jescarri/lora-sensor/src/lorawan_settings.hpp

#ifndef LORAWAN_SETTINGS_HPP_
#define LORAWAN_SETTINGS_HPP_
#include <FastLED.h>
#include <Preferences.h>
#include <lmic.h>

#include <hal/hal.h>

#define LMIC_PREF_NS_NAME "lmic"
#define LMIC_INIT_NEEDED_KEY_NAME "init"
#define LMIC_BYTES_KEY_NAME "lmic_struct"
#define LORAWAN_CONFIG_PRESENT_KEY "lorawan_config"
#define APP_EUID_KEY "euid"
#define MAX_LORAWAN_CONF_CHAR_LEN 100

#define RW_MODE false
#define RO_MODE true

extern lmic_t SETTINGS_LMIC;
extern Preferences lorawan_preferences;
extern lmic_t LMIC;
extern CRGB leds[1];

void lorawan_preferences_init();
void lmic_save();
bool lmic_init_needed();
void load_lmic();
void resetLmic();
bool lorawanConfigPresent();
int get_calibration_air_value();
int get_calibration_water_value();
int get_sleep_time_seconds();
#endif
